fietser28/EL-Load/connectors/EL-Load-Connectors-v3.png

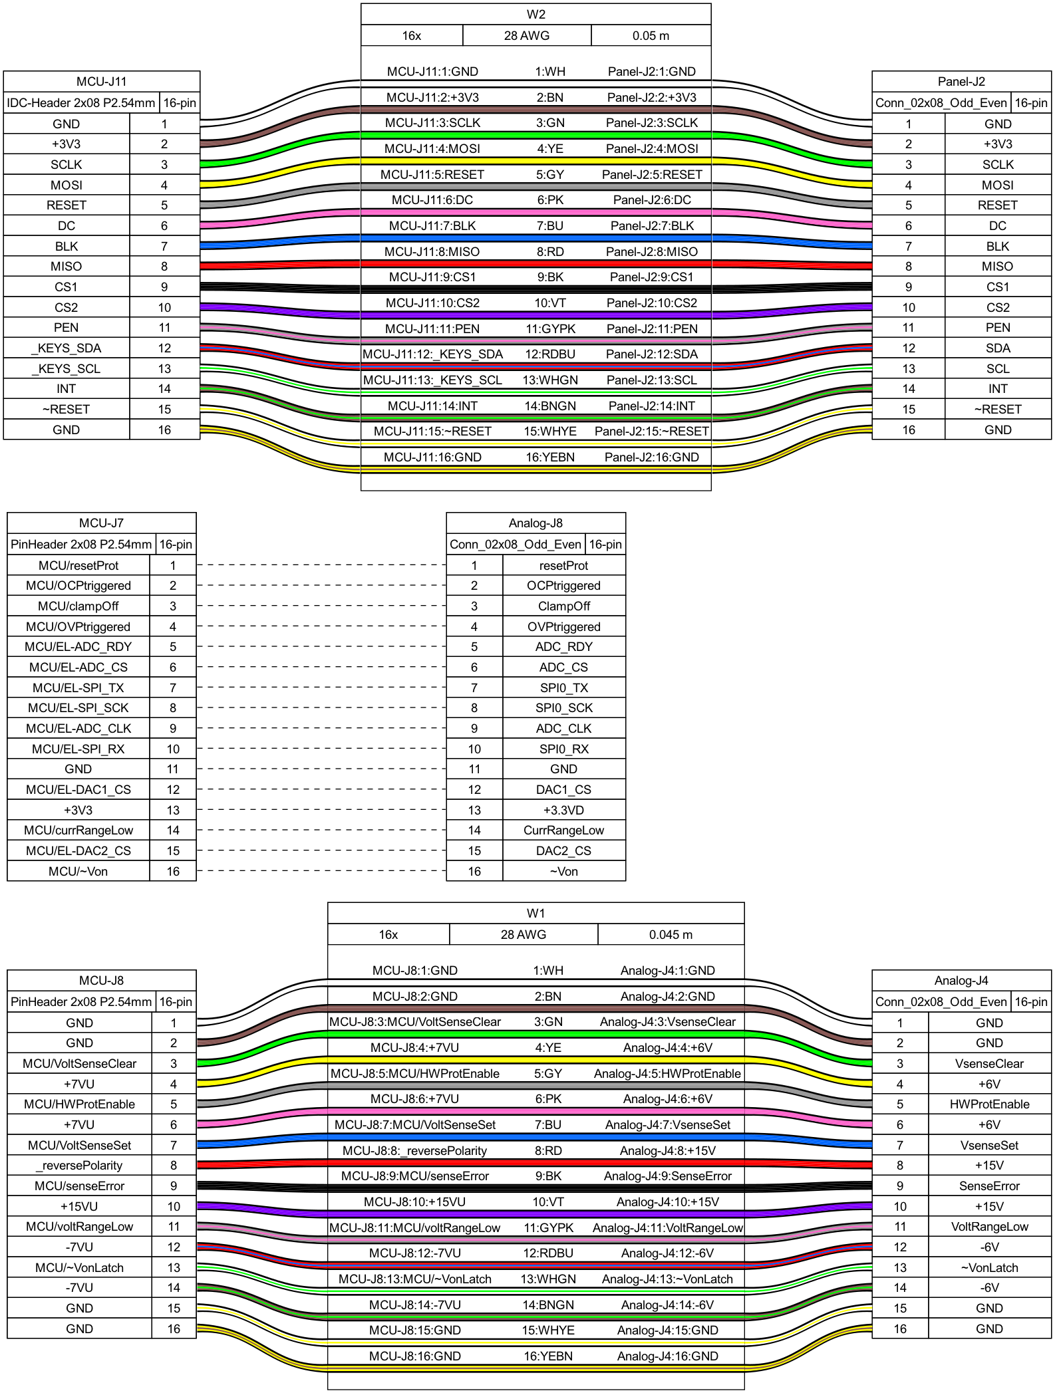
connectors/EL-Load-Connectors-v3.png
