fietser28/EL-Load/EL-Load-Analog/EL-Load-Analog-PCB-v4D.png

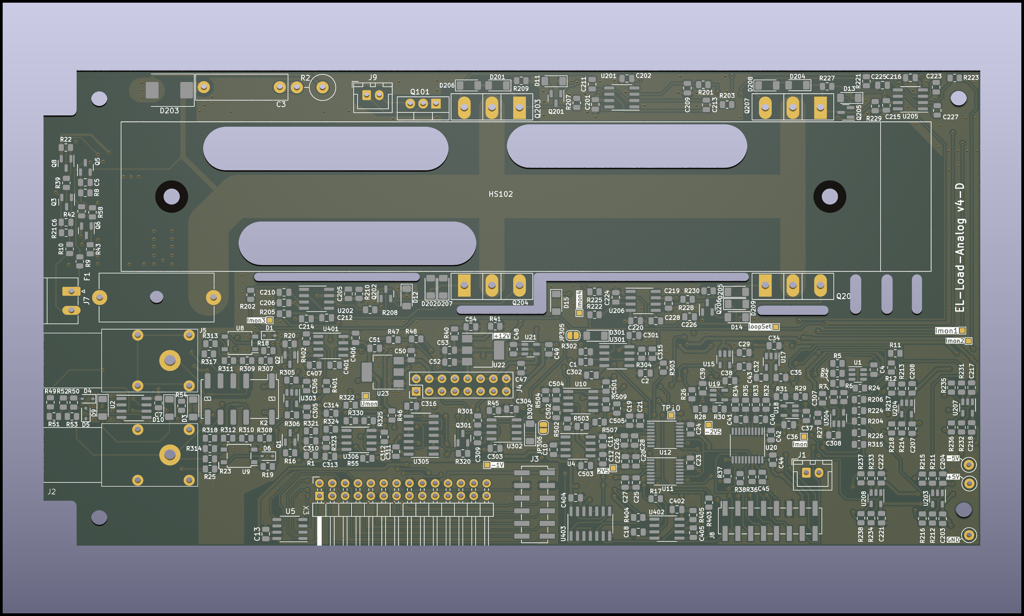
EL-Load-Analog/EL-Load-Analog-PCB-v4D.png
