fietser28/EL-Load/EL-Load-Digital/EL-Load-Digital-3D.jpg

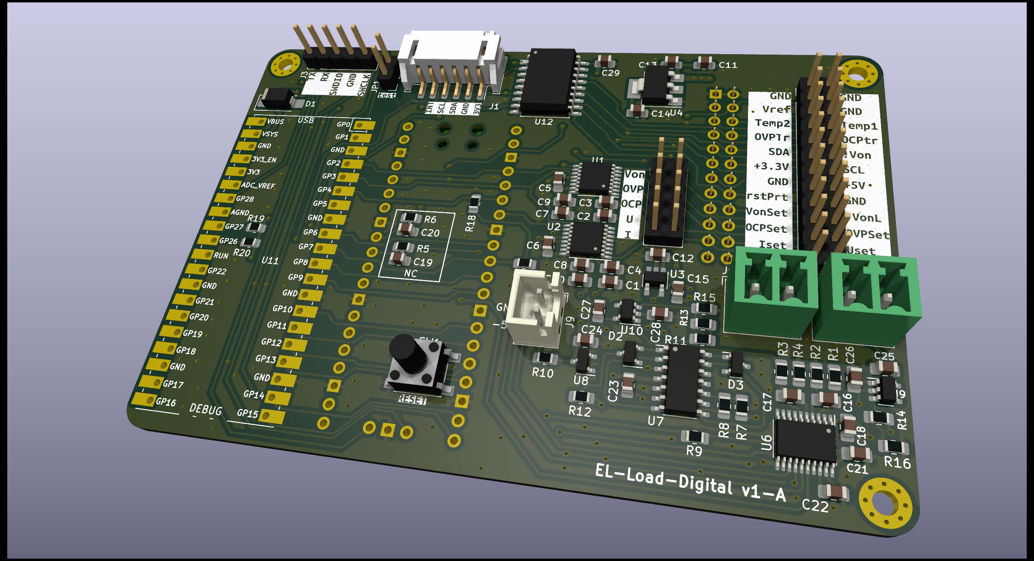
EL-Load-Digital/EL-Load-Digital-3D.jpg
