fietser28/EL-Load/3Dmodels/Standalone/Encoder knob.FCStd

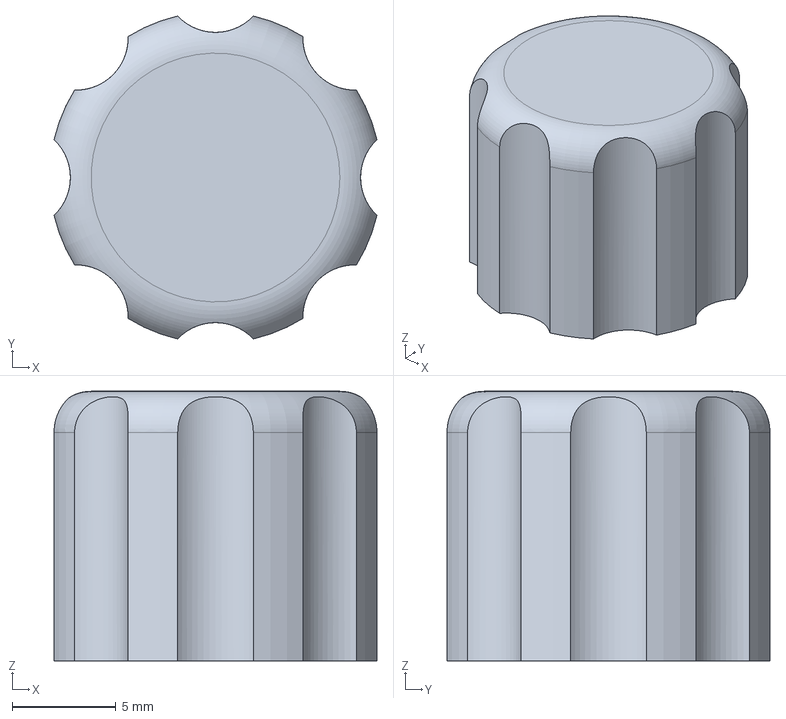
[picture p32: CAD file, 2025-07-27]
3Dmodels/Standalone/Encoder knob.FCStd
15.6 x 15.6 x 13.0 mm
