fietser28/EL-Load/3Dmodels/PCB-stands/PCB-Fan-Controller-BodyThickness.stl

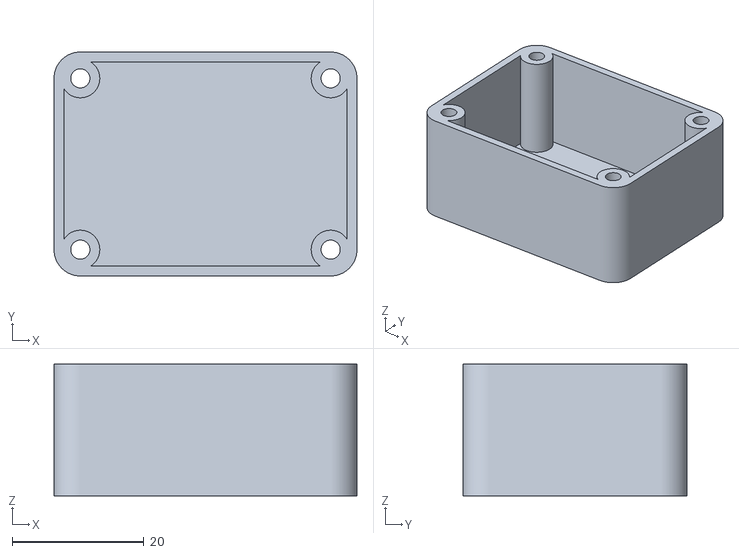
[picture p33: CAD file, 2023-12-24]
3Dmodels/PCB-stands/PCB-Fan-Controller-BodyThickness.stl
46.0 x 34.0 x 20.0
