fietser28/EL-Load/3Dmodels/Standalone/BevelHinge.FCStd

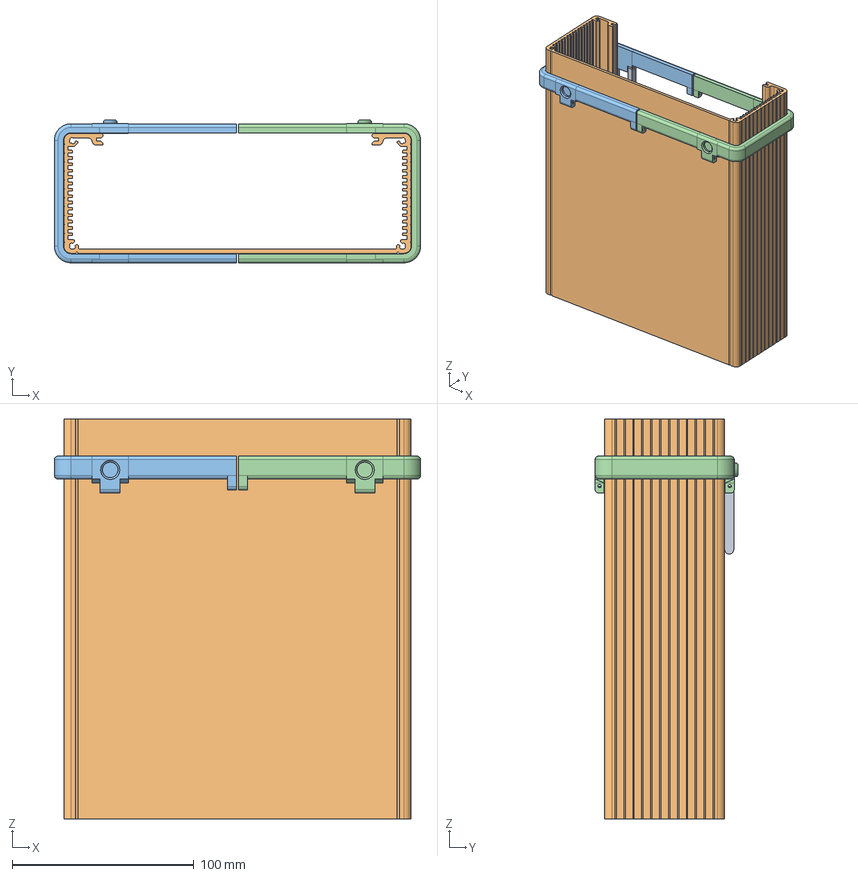
[picture p34: CAD file, 2025-02-22]
3Dmodels/Standalone/BevelHinge.FCStd
201.5 x 78.6 x 220.0 mm
Hinge
U extrusion 220mm
Bevel
BevelMirror
