fietser28/EL-Load/3Dmodels/PCB-stands/PCB-EL-Load-Digital.FCStd

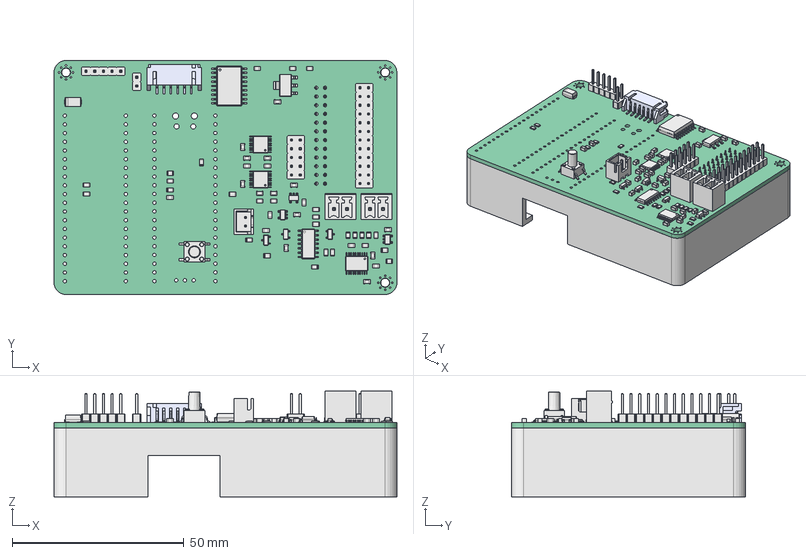
[picture p35: CAD file, 2023-12-24]
3Dmodels/PCB-stands/PCB-EL-Load-Digital.FCStd
100.0 x 68.3 x 30.8 mm
Pcb_76d8
R5_R_0805_2012Metric_c332fffaa67e x 20
D3_SOT_23_f131065e1f10 x 3
C21_C_0805_2012Metric_70c36fc92965 x 29
U2_TSSOP_16_44x5mm_P065mm_5dc6f22c2fcc x 2
JP1_PinHeader_1x02_P254mm_Vertical_bab78b325c3c
U12_SOIC_18W_75x116mm_P127mm_c252929a2548
U6_TSSOP_20_44x65mm_P065mm_4278e9939631
J8_PinHeader_2x05_P254mm_Vertical_9893bb5028ab
J4_PinHeader_2x12_P254mm_Vertical_3dcfa0b37e50
U7_SOIC_14_39x87mm_P127mm_ab895dfdb68d
J7_MCV_01x02_G_3_81mm_600c88b03bf4 x 2
U3_SOT_23_5_d6b5d491d0c5 x 3
D1_D_SMA_e9ef64f25d9d
J9_JST_B2B_XH_A_4d0ab671784d
J3_PinHeader_1x05_P254mm_Vertical_ee2410f2d2c0
SW1_Tactal Switch - SMD (6mmx 6mmx__mm) - Marked_5d5b019a6e61[2]
U4_SOT_223_77804c9ac5c6
J2_PinSocket_2x12_P254mm_Vertical_20041d601904
