fietser28/EL-Load/3Dmodels/Standalone/EL-Load-CaseV4-cover.stl

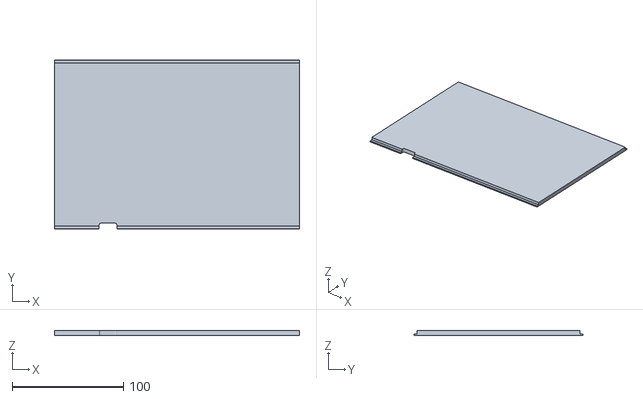
[picture p36: CAD file, 2024-11-03]
3Dmodels/Standalone/EL-Load-CaseV4-cover.stl
220.0 x 152.2 x 4.29
