fietser28/EL-Load/3Dmodels/PCB-stands/PCB-PowerTest1.FCStd

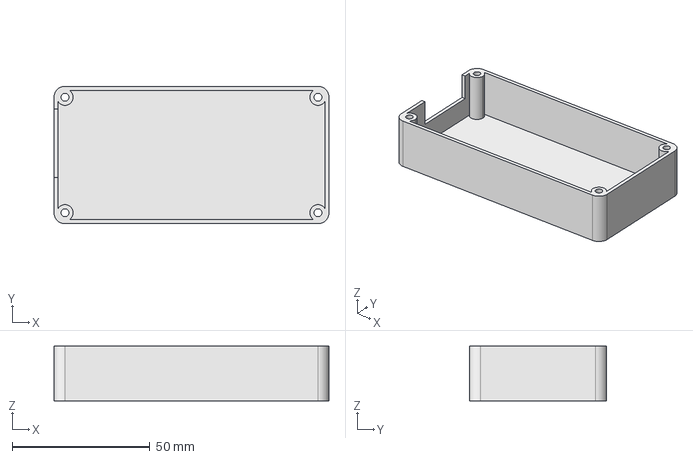
[picture p37: CAD file, 2023-12-24]
3Dmodels/PCB-stands/PCB-PowerTest1.FCStd
100.0 x 50.0 x 20.0 mm
