fietser28/EL-Load/3Dmodels/Standalone/EL-Load-CaseV4-Front Panel.stl

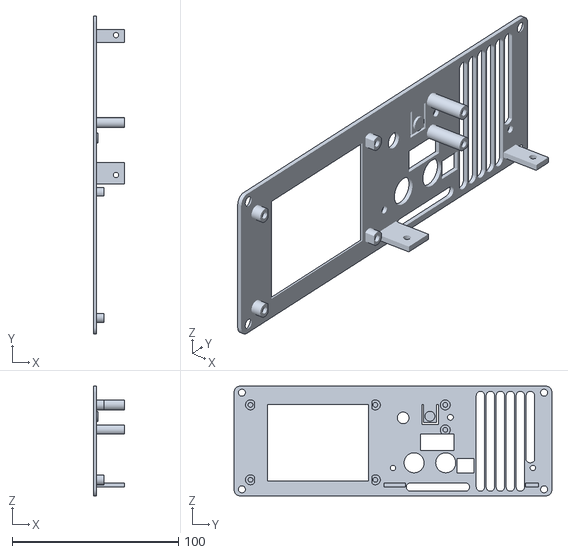
[picture p38: CAD file, 2024-11-03]
3Dmodels/Standalone/EL-Load-CaseV4-Front Panel.stl
18.8 x 191.0 x 66.0
