fietser28/EL-Load/3Dmodels/Standalone/EL-Load-CaseV4-RearPanel.stl

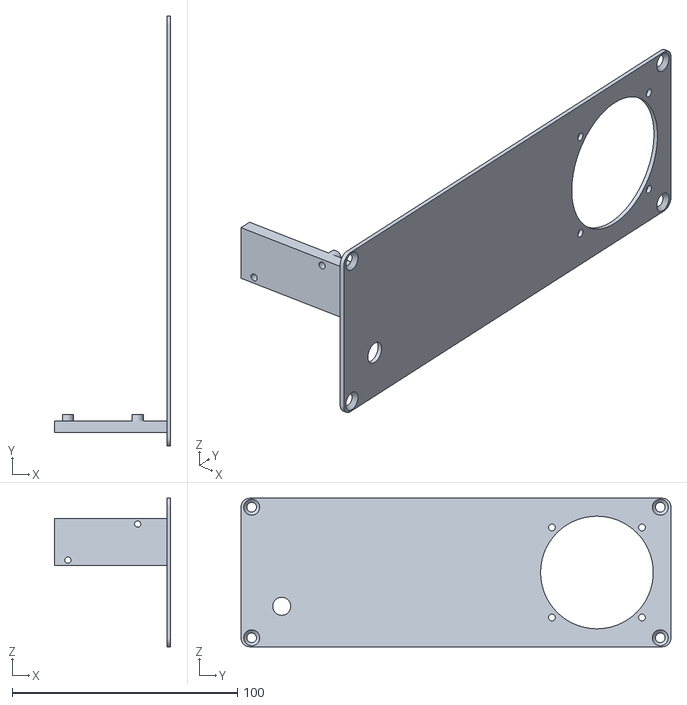
[picture p39: CAD file, 2024-11-03]
3Dmodels/Standalone/EL-Load-CaseV4-RearPanel.stl
51.6 x 191.0 x 66.0
