fietser28/EL-Load/3Dmodels/Standalone/BevelHinge-Hinge.stl

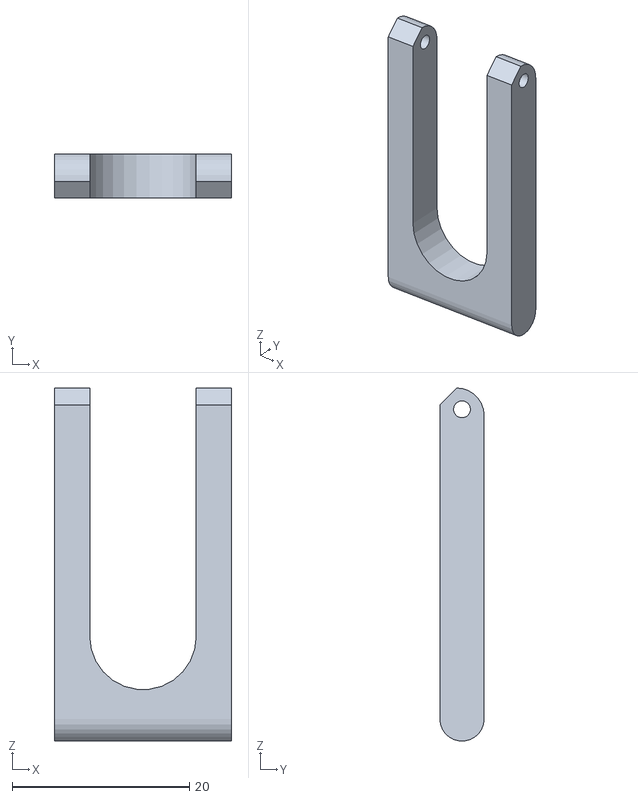
[picture p40: CAD file, 2024-11-03]
3Dmodels/Standalone/BevelHinge-Hinge.stl
20.0 x 5.00 x 39.8
