fietser28/EL-Load/3Dmodels/PCB-stands/PCB-EL-Load-Analog-Fan30Stand2.FCStd

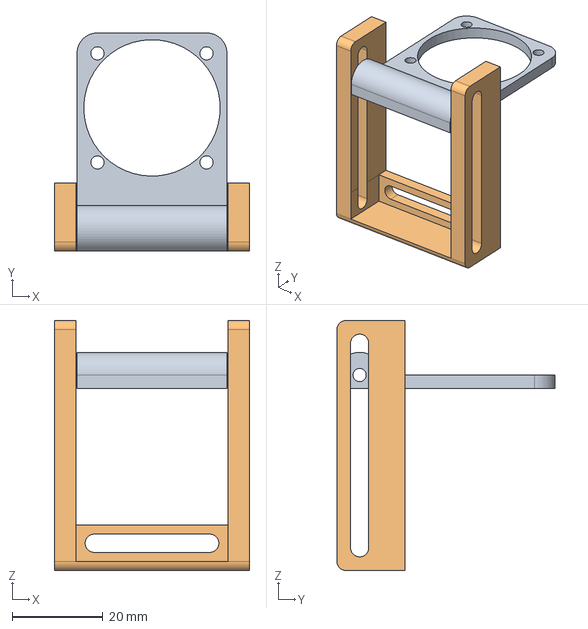
[picture p41: CAD file, 2023-12-24]
3Dmodels/PCB-stands/PCB-EL-Load-Analog-Fan30Stand2.FCStd
43.0 x 48.0 x 55.0 mm
FanBracket
FanSupport
