fietser28/EL-Load/3Dmodels/Standalone/BevelHinge-BevelMirror.stl

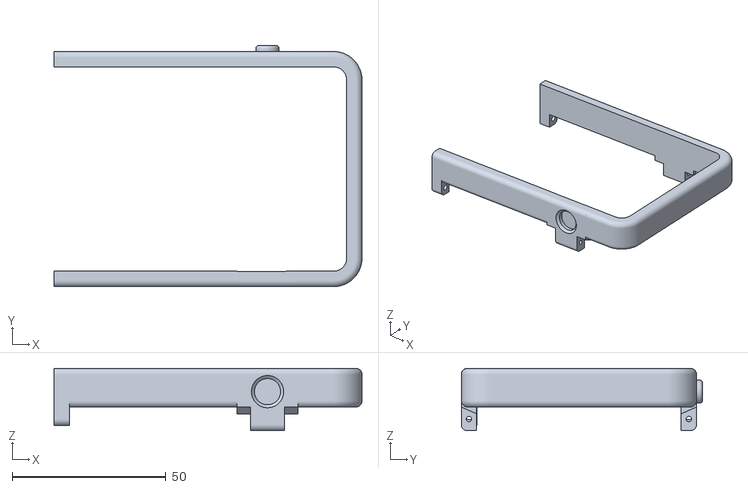
[picture p42: CAD file, 2024-11-03]
3Dmodels/Standalone/BevelHinge-BevelMirror.stl
100.3 x 78.6 x 20.3
