fietser28/EL-Load/3Dmodels/PCB-stands/PCB-EL-Load-Digital-Body.stl

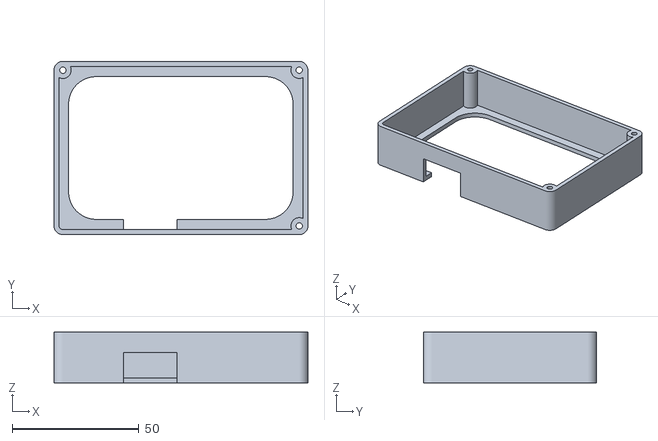
[picture p43: CAD file, 2023-12-24]
3Dmodels/PCB-stands/PCB-EL-Load-Digital-Body.stl
100.0 x 68.2 x 20.0
