fietser28/EL-Load/3Dmodels/PCB-stands/PCB-EL-Load-Analog-PartPad001.stl

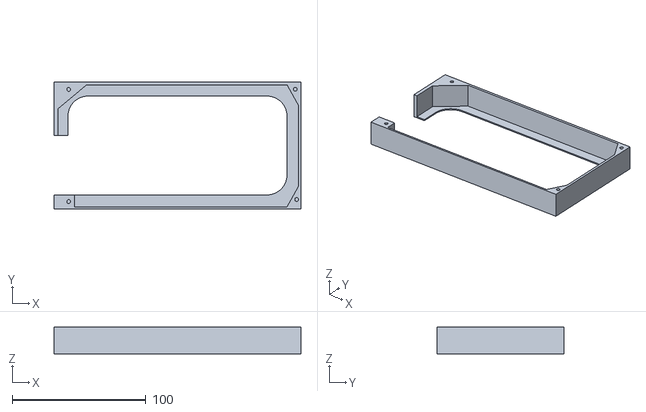
[picture p44: CAD file, 2023-12-24]
3Dmodels/PCB-stands/PCB-EL-Load-Analog-PartPad001.stl
185.0 x 95.0 x 20.0
