fietser28/EL-Load/3Dmodels/PCB-stands/PCB-EL-Load-Simple-Power.FCStd

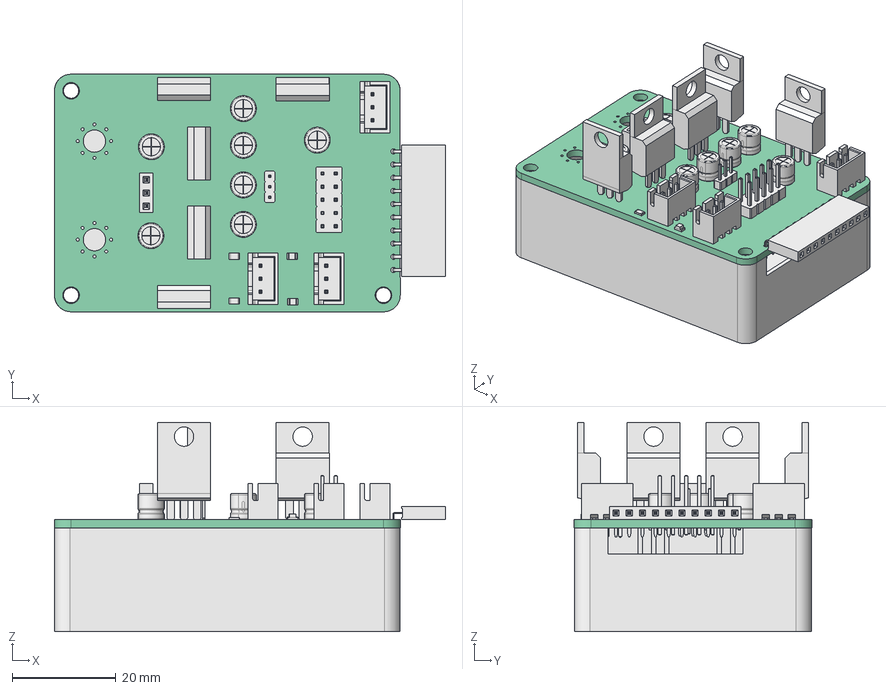
[picture p45: CAD file, 2023-12-24]
3Dmodels/PCB-stands/PCB-EL-Load-Simple-Power.FCStd
75.4 x 45.8 x 40.4 mm
Pcb_f12
C2_CP_Radial_D50mm_P200mm_86e44747657e x 7
J2_PinHeader_2x05_P254mm_Vertical_2d928ccc9e48
U5_TO-220-3_Vertical_5d7781ab892e x 5
J4_PinSocket_1x10_P254mm_Horizontal_80075c0270da
J3_JST_B3B_XH_A_405c3f21dcc5 x 3
R2_R_0805_2012Metric_513d5d51fc14 x 2
D1_LED_0805_2012Metric_2fdb85feb49a x 2
J1_PinHeader_1x03_P200mm_Vertical_4dd7be2cd8ec
U1_PinSocket_1x03_P254mm_Vertical_91df090aab00
