fietser28/EL-Load/3Dmodels/PCB-stands/PCB-ADS1115-module.FCStd

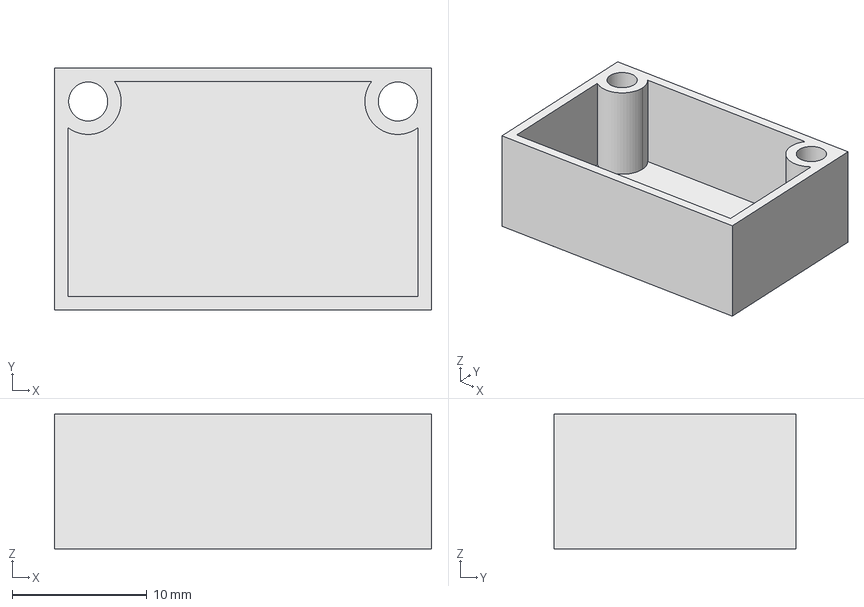
[picture p46: CAD file, 2023-12-24]
3Dmodels/PCB-stands/PCB-ADS1115-module.FCStd
28.0 x 18.0 x 10.0 mm
