fietser28/EL-Load/3Dmodels/PCB-stands/PCB-EL-Load-Analog-Fan30Stand2-FanBracket.stl

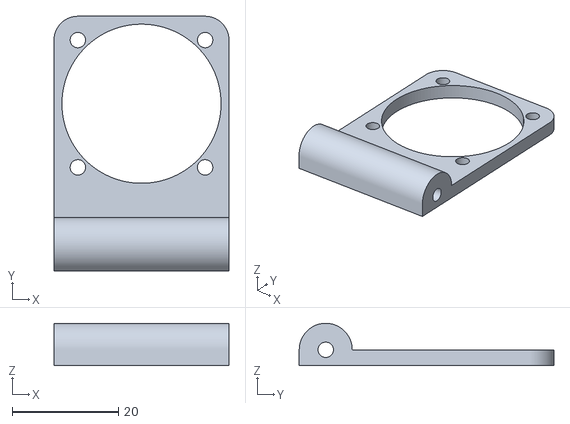
[picture p47: CAD file, 2023-12-24]
3Dmodels/PCB-stands/PCB-EL-Load-Analog-Fan30Stand2-FanBracket.stl
33.0 x 48.0 x 8.00
