fietser28/EL-Load/3Dmodels/PCB-stands/PCB-EL-Load-Analog-NTCclip.FCStd

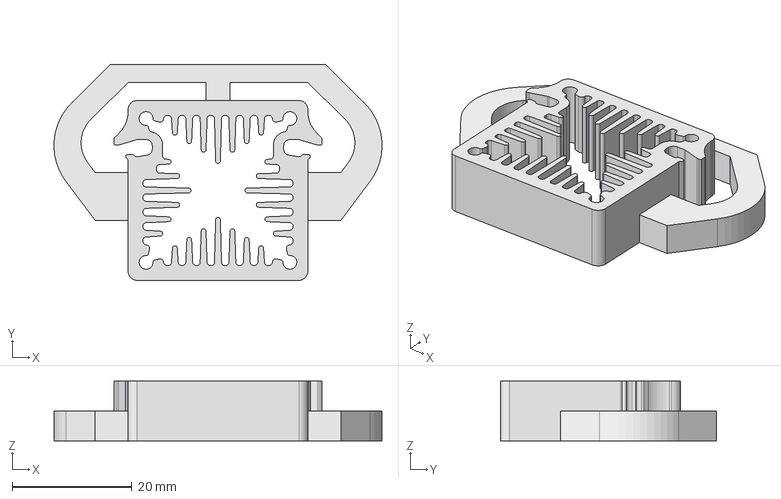
[picture p48: CAD file, 2023-12-24]
3Dmodels/PCB-stands/PCB-EL-Load-Analog-NTCclip.FCStd
54.7 x 36.0 x 10.0 mm
LAM_3_K
