fietser28/EL-Load/EL-Load-Analog/3Dmodels/schutzinger-sweb-8094-isolated-banana-jack-pcb-1kv-24a-1/SWEB 8094 Assembly.png

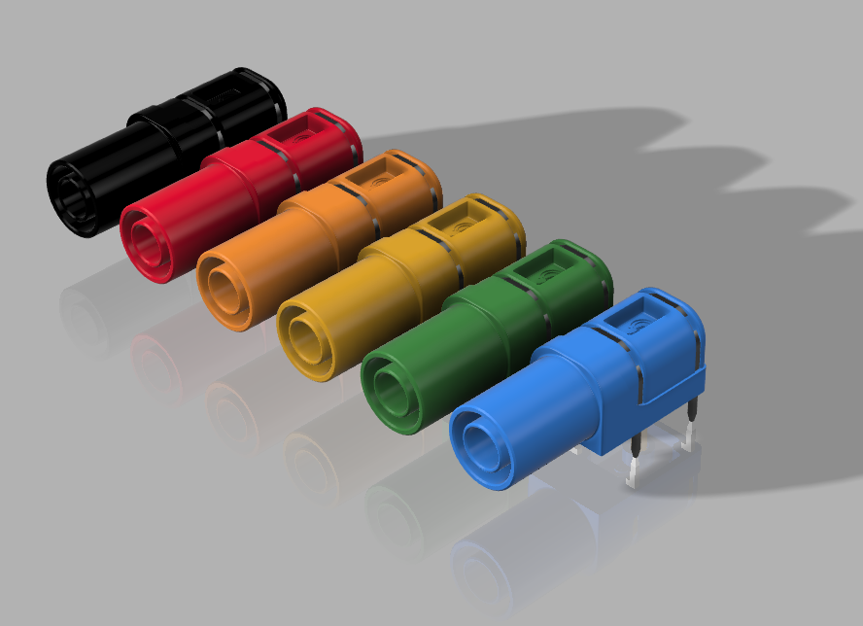
EL-Load-Analog/3Dmodels/schutzinger-sweb-8094-isolated-banana-jack-pcb-1kv-24a-1/SWEB 8094 Assembly.png
