fietser28/EL-Load/Obsolete/EL-Load-Reverse-Polarity/EL-Load-Reverse-Polarity-v2.pdf

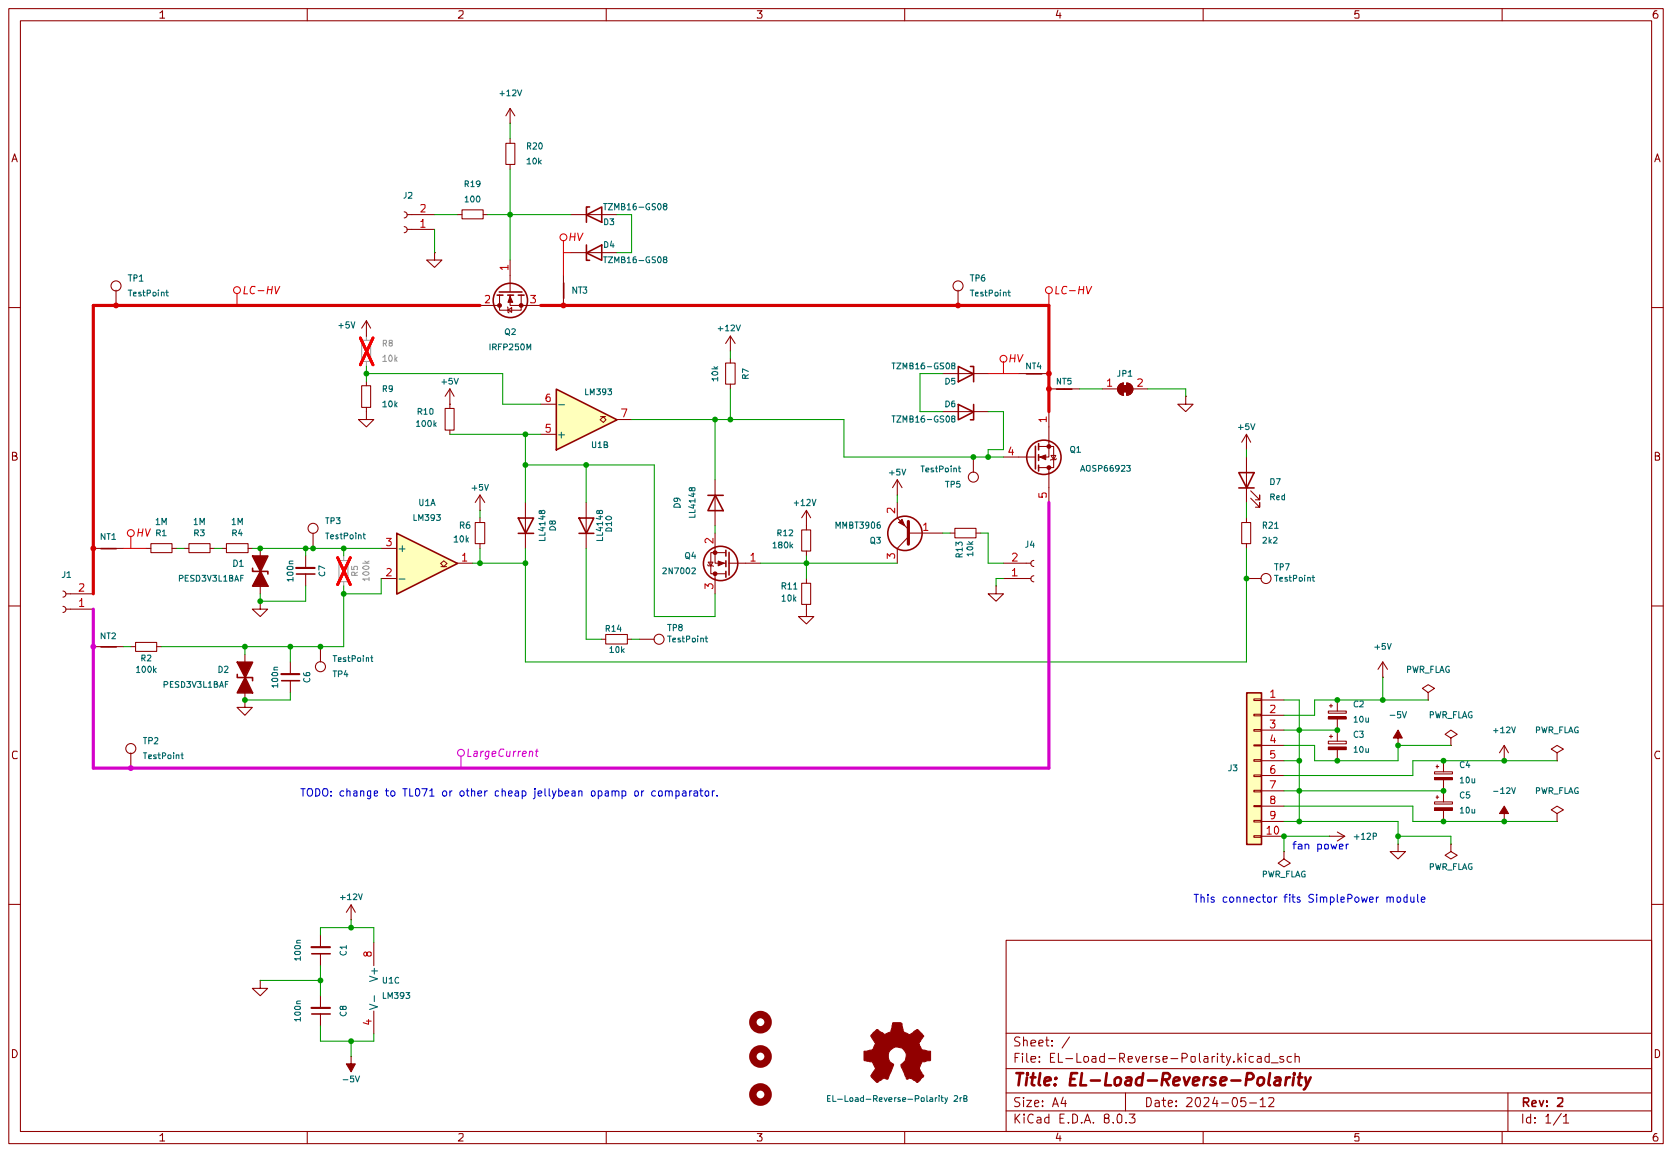
[picture p83: page 1]
