fietser28/EL-Load/Obsolete/EL-Load-Reverse-Polarity/EL-Load-Reverse-Polarity-v1.pdf

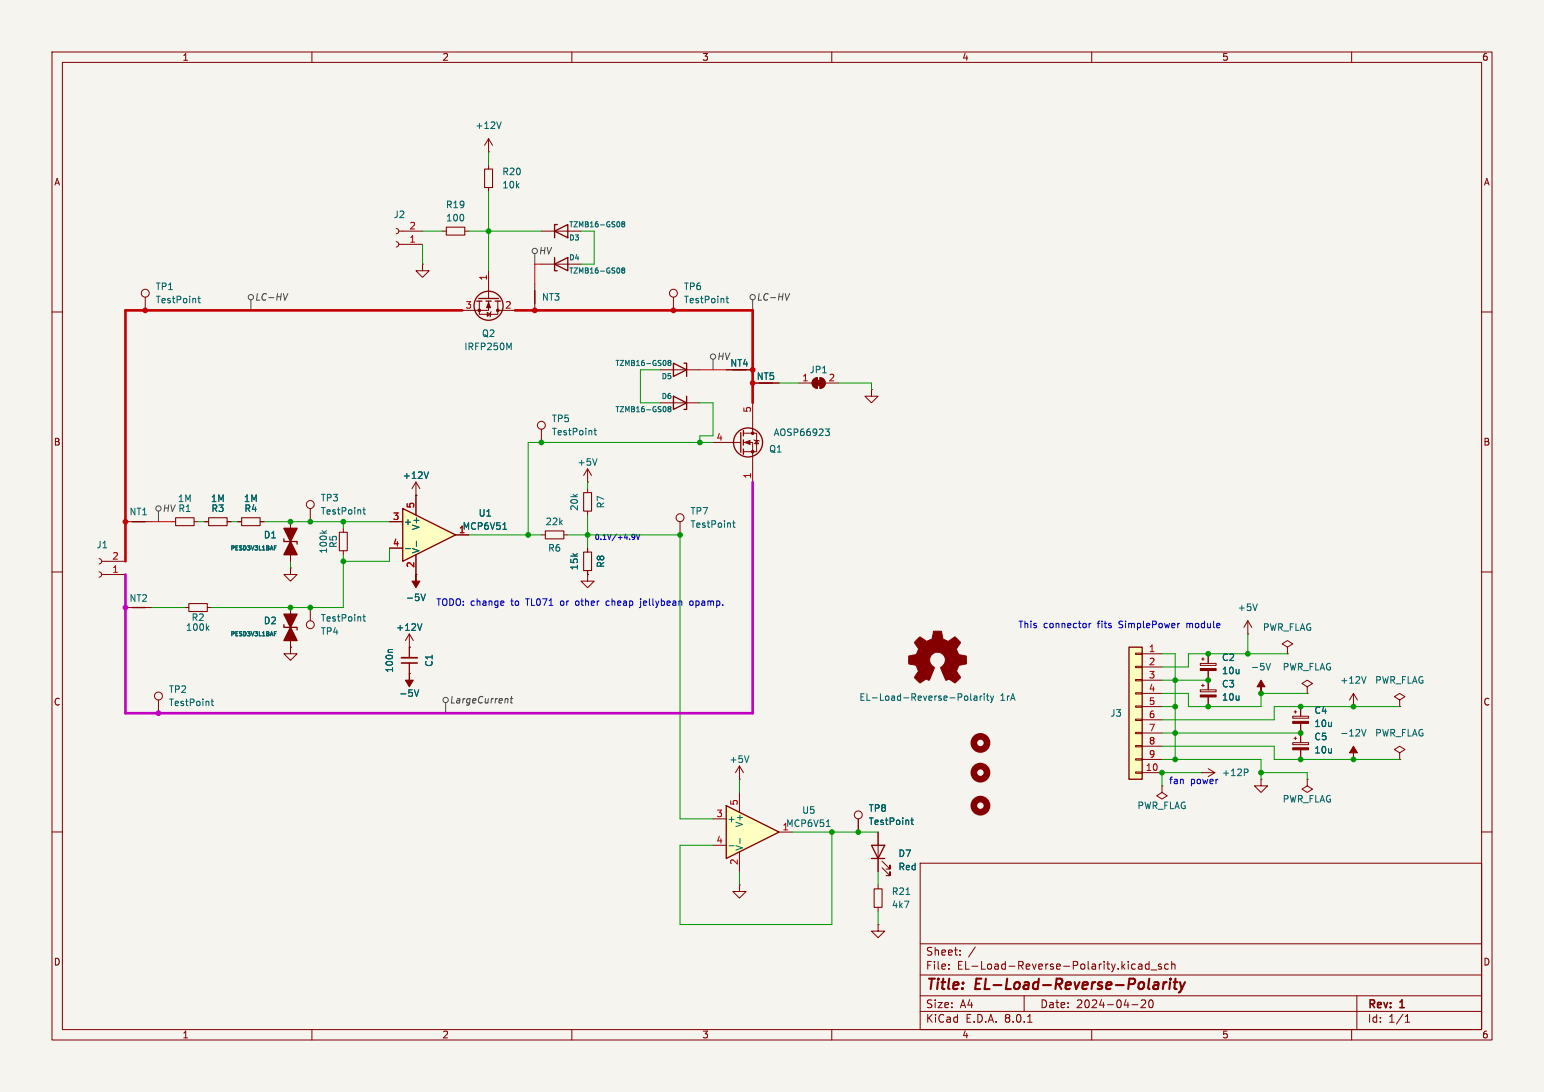
[picture p84: page 1]

Id: 1/1 Title: EL-Load-Reverse-Polarity
